zhenga1/Anodroid/Process Solidworks Version 6/2020-03-10_222859.png

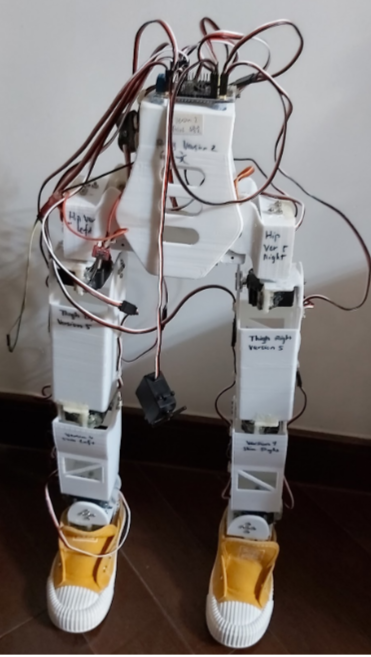
Process Solidworks Version 6/2020-03-10_222859.png
