zhenga1/Anodroid/Process Solidworks Version 6/Motor assem new with axis.SLDASM

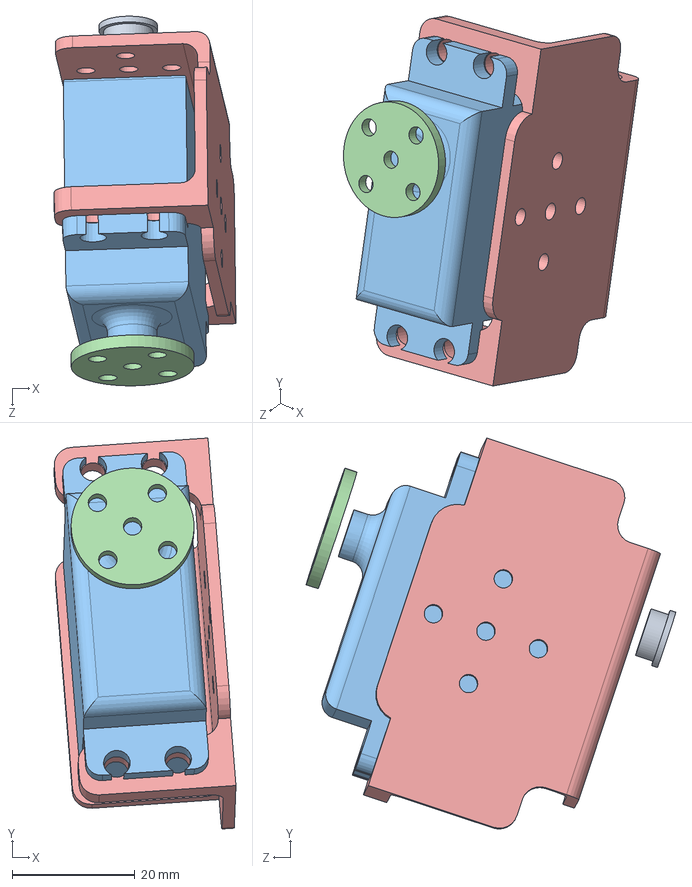
[picture p9: CAD file, 2020-06-27]
Process Solidworks Version 6/Motor assem new with axis.SLDASM
29.6 x 63.6 x 60.1 mm
Holder Right
Top of motor-SR1501
Motor SR-1501
Assisting axis part
Major Axis
