zhenga1/Anodroid/Process Solidworks Newest/Motor assem new with axis.SLDASM

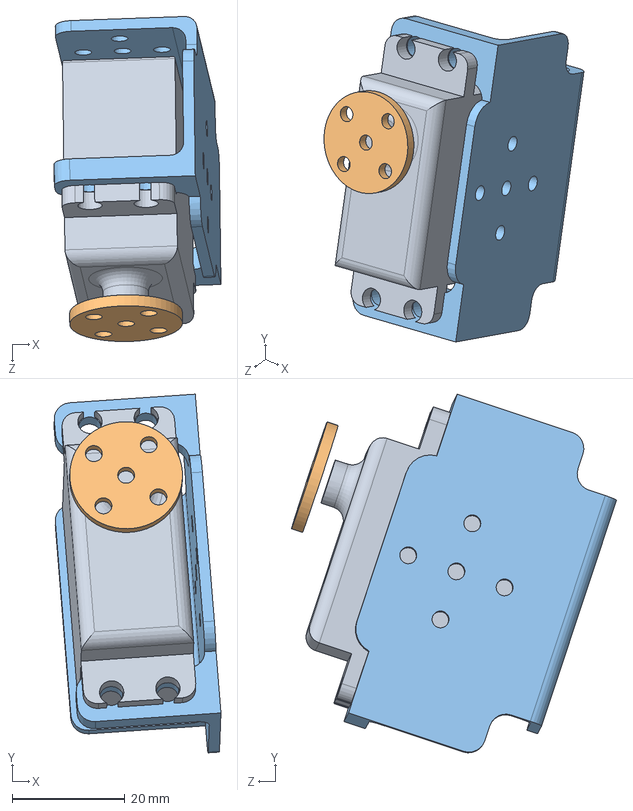
[picture p14: CAD file, 2020-06-27]
Process Solidworks Newest/Motor assem new with axis.SLDASM
29.6 x 63.6 x 57.6 mm
Holder Right
Top of motor-SR1501
Motor SR-1501
