zhenga1/Anodroid/Process Solidworsk version 3(incomplete)/Assemcomplete.SLDASM

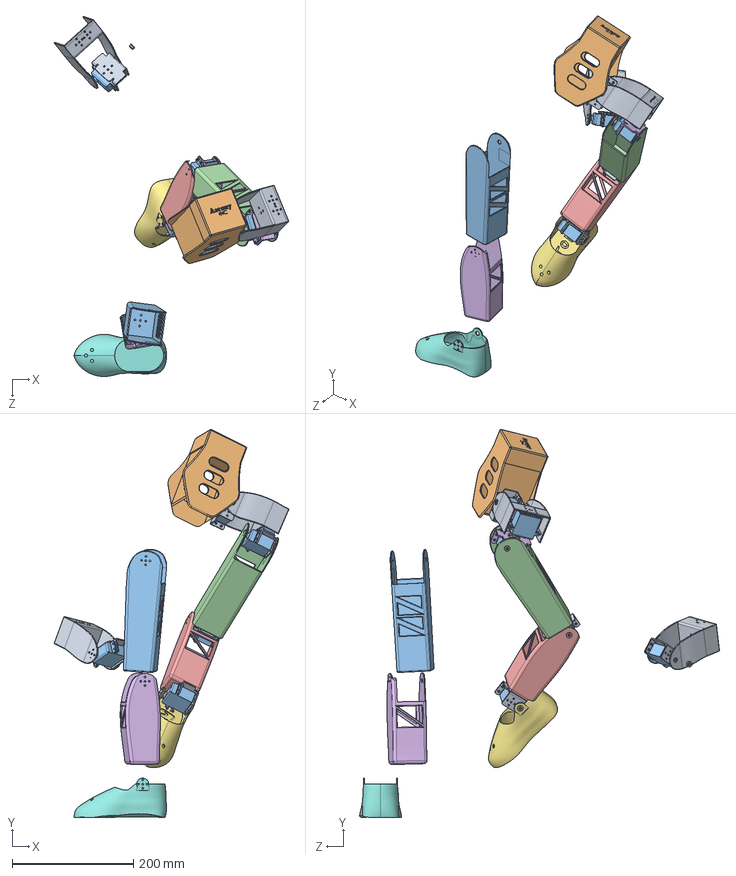
[picture p22: CAD file, 2020-06-27]
Process Solidworsk version 3(incomplete)/Assemcomplete.SLDASM
386.8 x 639.6 x 593.3 mm
pelvisthing
Thigh left
ThighFirst
Shinmy
Shincpy
Foot
Foot left
Holder x 5
Top of motor-SR1501 x 6
Motor SR-1501 x 6
Assisting axis part x 4
Major Axis x 5
Holder - Copy
