zhenga1/Anodroid/Process Solidworks Version 6/Replacement Temporary.SLDASM

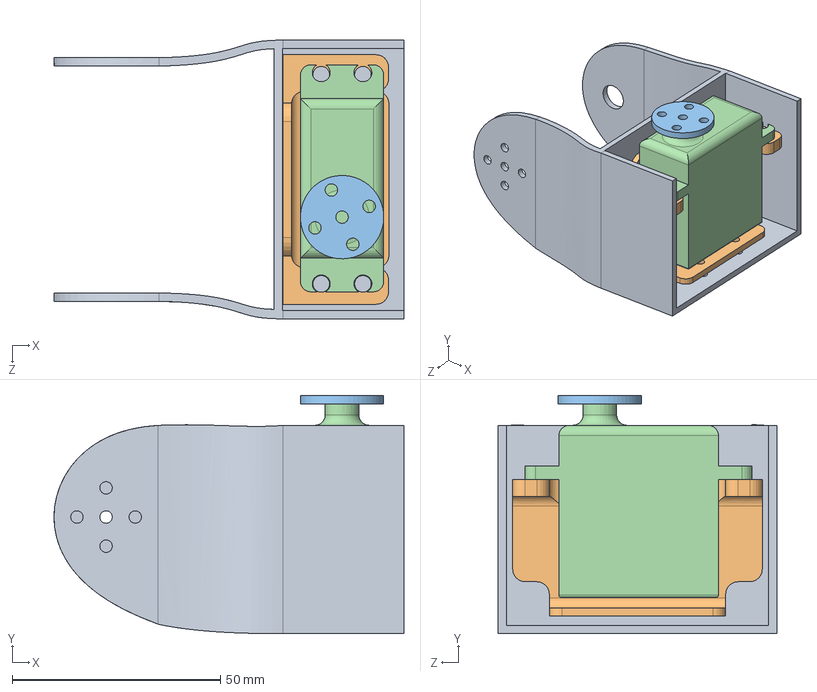
[picture p23: CAD file, 2020-06-27]
Process Solidworks Version 6/Replacement Temporary.SLDASM
84.0 x 57.2 x 66.9 mm
hip v5
Holder Right
Top of motor-SR1501
Motor SR-1501
