zhenga1/Anodroid/Process Solidworks Version 6/Motor assem modified right.SLDASM

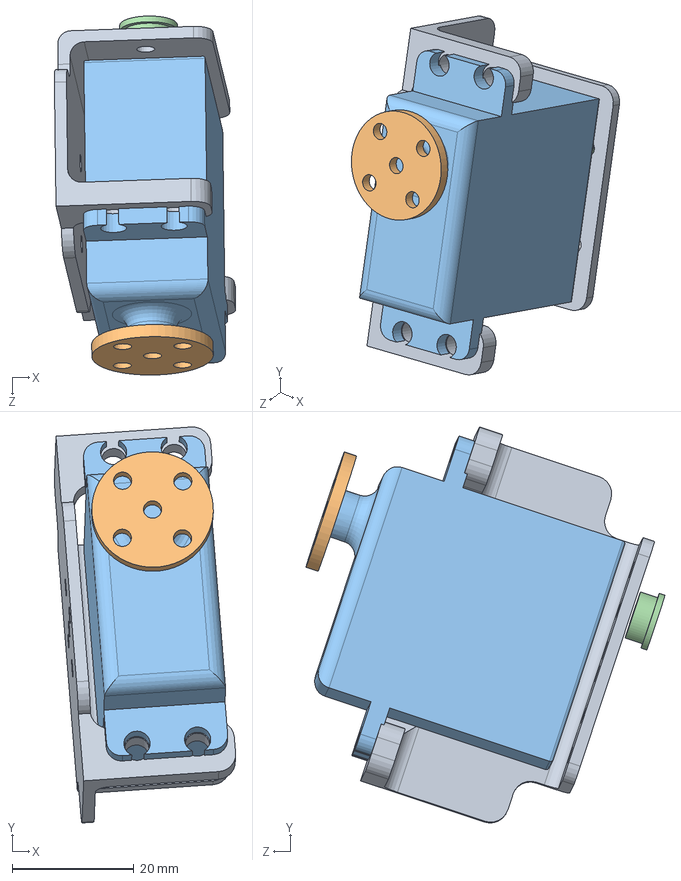
[picture p24: CAD file, 2020-06-27]
Process Solidworks Version 6/Motor assem modified right.SLDASM
29.8 x 65.1 x 59.1 mm
Top of motor-SR1501
Motor SR-1501
Holder Left
Major Axis
