zhenga1/Anodroid/Process Solidworks Newest/Hip-test-main.SLDASM

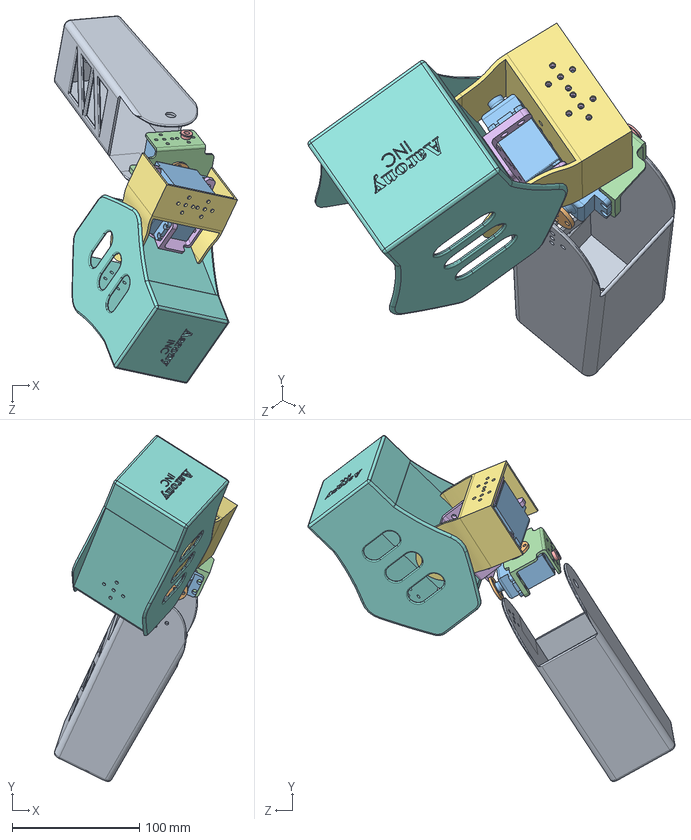
[picture p25: CAD file, 2020-06-27]
Process Solidworks Newest/Hip-test-main.SLDASM
143.9 x 271.9 x 288.4 mm
ThighFirst
Top of motor-SR1501 x 3
Motor SR-1501 x 3
Holder - Copy
Major Axis
Holder x 2
pelvisthing
