zhenga1/Anodroid/Process Solidworks Version 6/Motor assem left.SLDASM

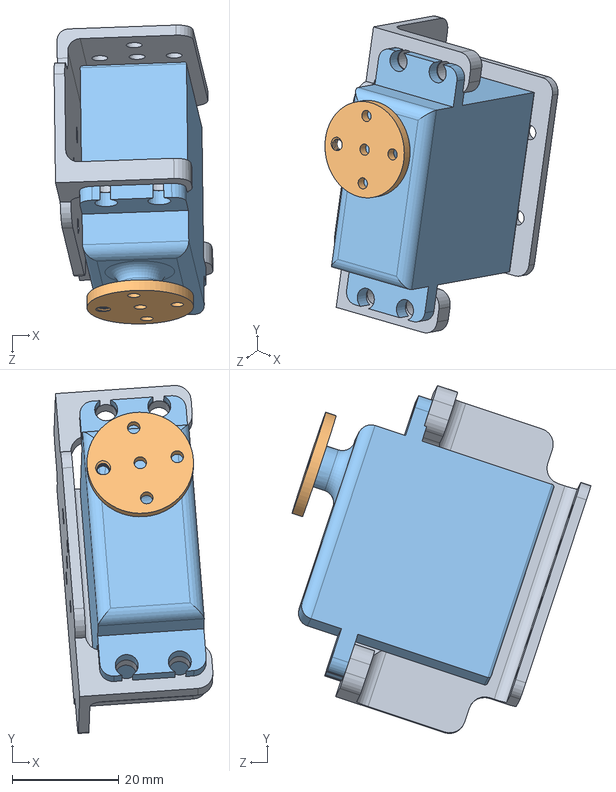
[picture p26: CAD file, 2020-06-27]
Process Solidworks Version 6/Motor assem left.SLDASM
29.8 x 65.3 x 56.1 mm
Top of motor-SR1501
Motor SR-1501
Holder Right
