zhenga1/Anodroid/Process Solidworsk version 3(incomplete)/Thigh Motor assem.SLDASM

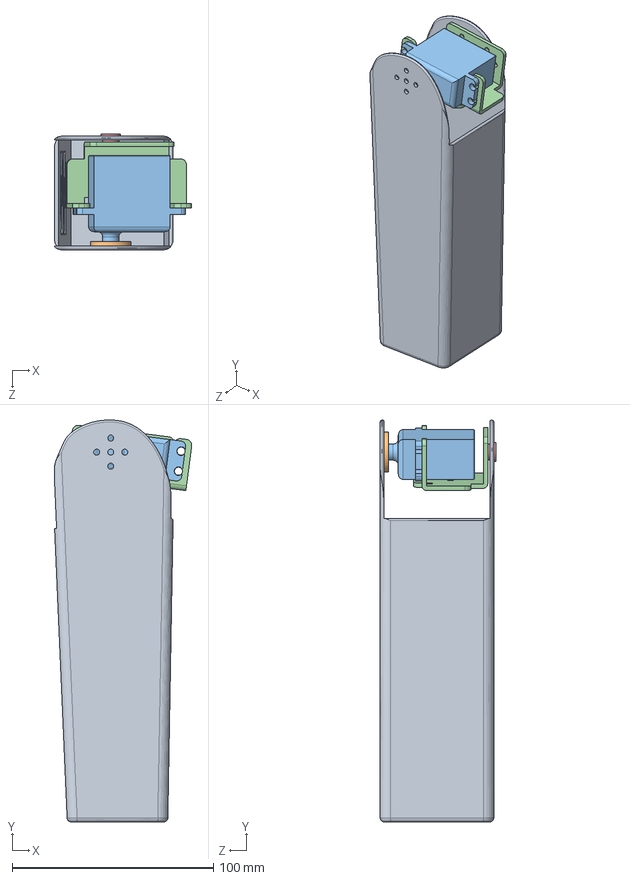
[picture p27: CAD file, 2019-08-12]
Process Solidworsk version 3(incomplete)/Thigh Motor assem.SLDASM
68.4 x 200.0 x 57.5 mm
ThighFirst
Top of motor-SR1501
Motor SR-1501
Holder - Copy
Major Axis
