zhenga1/Anodroid/Process Solidworsk version 3(incomplete)/Shincpy.SLDPRT

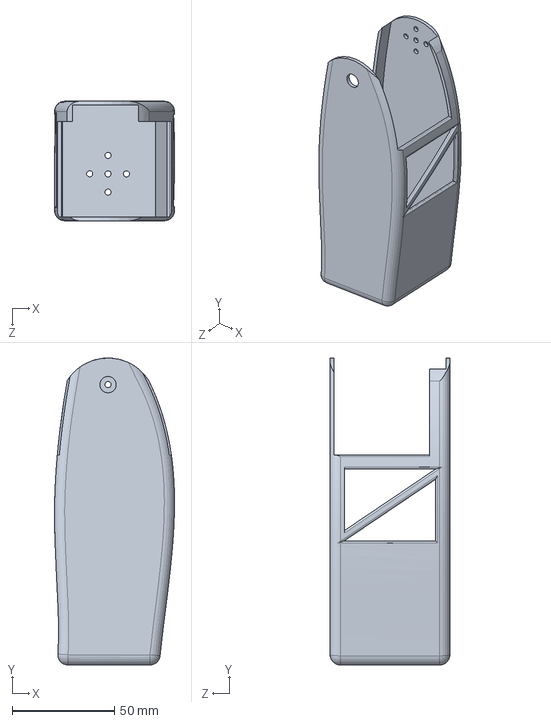
[picture p28: CAD file, 2020-06-27]
Process Solidworsk version 3(incomplete)/Shincpy.SLDPRT
58.7 x 150.0 x 58.5 mm
