zhenga1/Anodroid/Process Solidworks Version 6/hip v6.SLDPRT

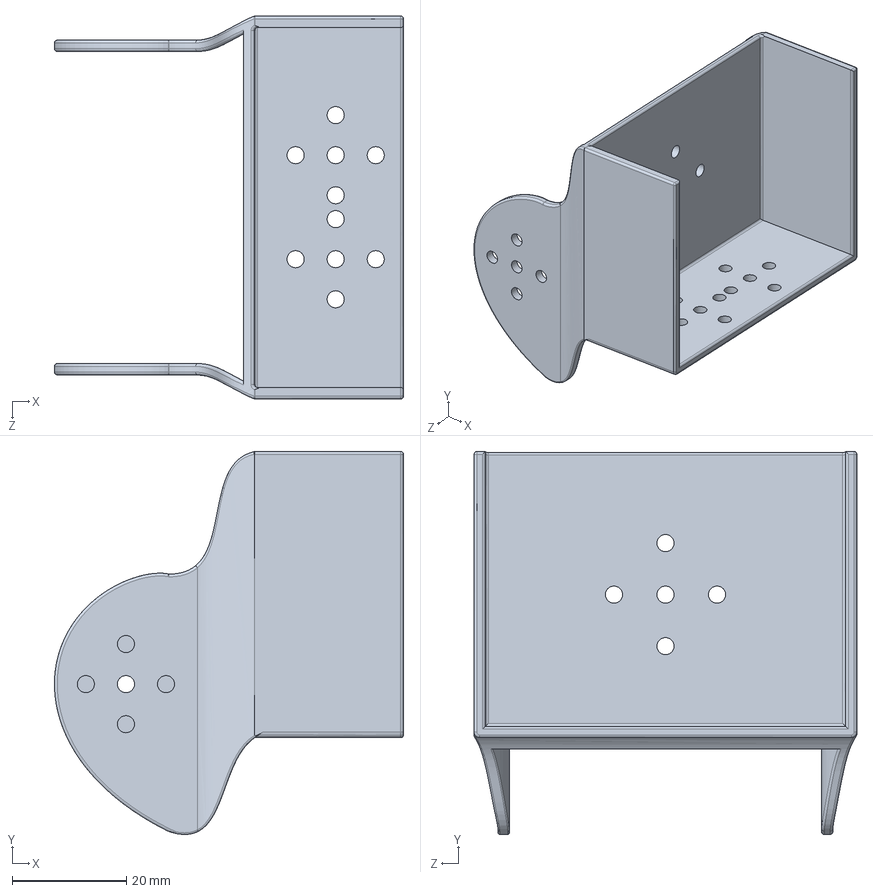
[picture p29: CAD file, 2020-06-27]
Process Solidworks Version 6/hip v6.SLDPRT
61.0 x 66.9 x 66.9 mm
