zhenga1/Anodroid/Process Solidworsk version 3(incomplete)/Foot.SLDPRT

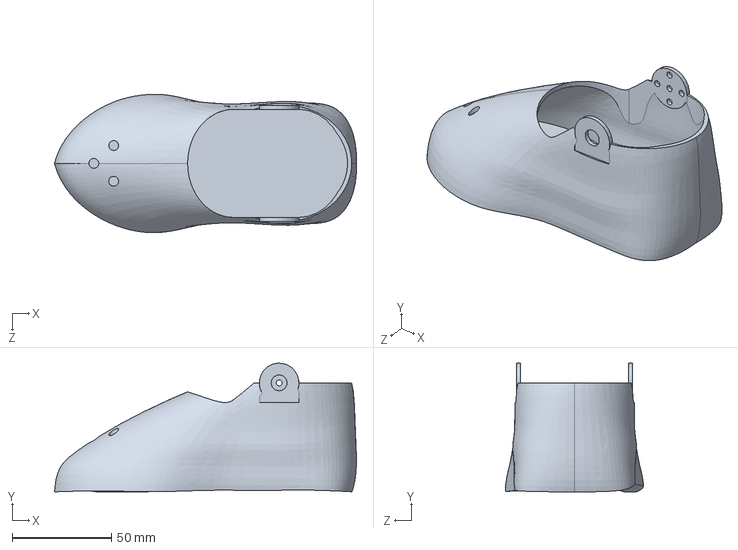
[picture p30: CAD file, 2020-06-27]
Process Solidworsk version 3(incomplete)/Foot.SLDPRT
152.4 x 65.0 x 69.8 mm
