zhenga1/Anodroid/Process Solidworks Version 6/pelvisthing.SLDPRT

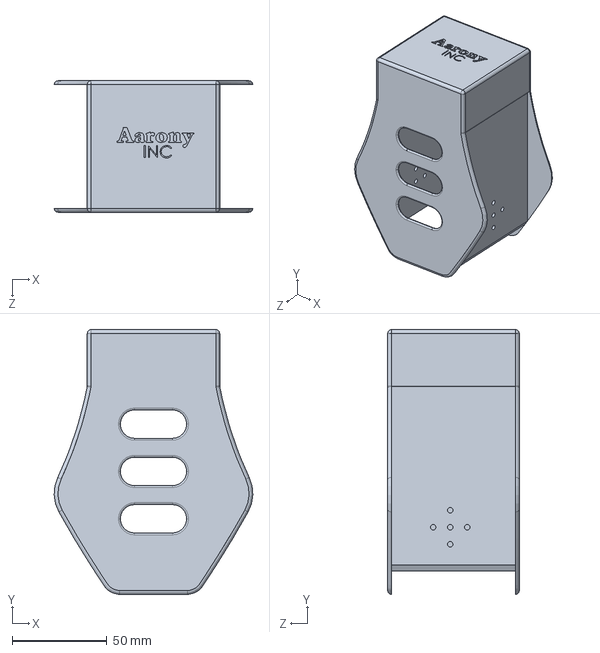
[picture p31: CAD file, 2020-06-27]
Process Solidworks Version 6/pelvisthing.SLDPRT
105.0 x 140.0 x 69.5 mm
