zhenga1/Anodroid/Process Solidworks Newest/Shincpy.SLDPRT

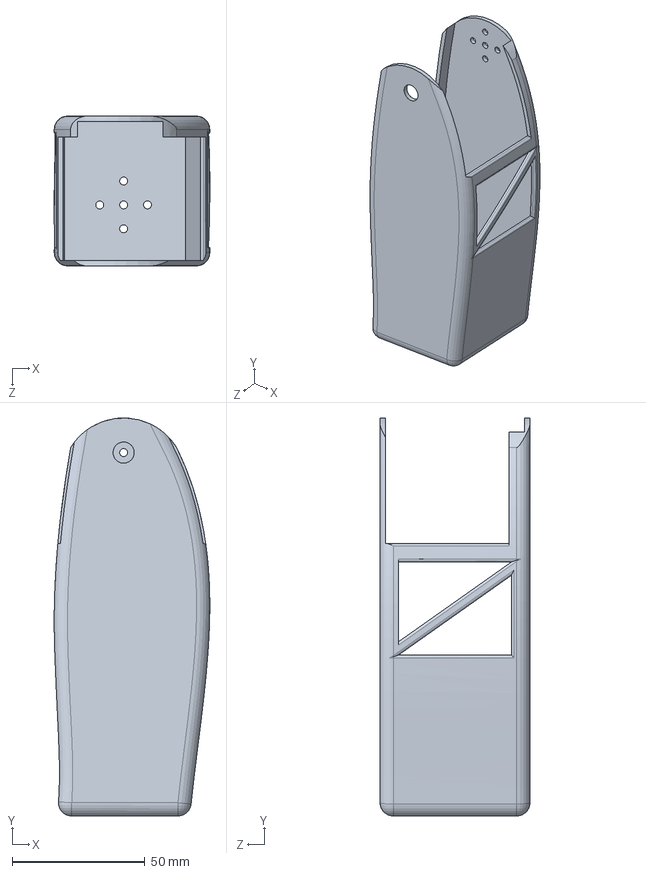
[picture p32: CAD file, 2020-06-27]
Process Solidworks Newest/Shincpy.SLDPRT
58.7 x 150.0 x 56.5 mm
