zhenga1/Anodroid/Process Solidworks Version 6/Holder Left.SLDPRT

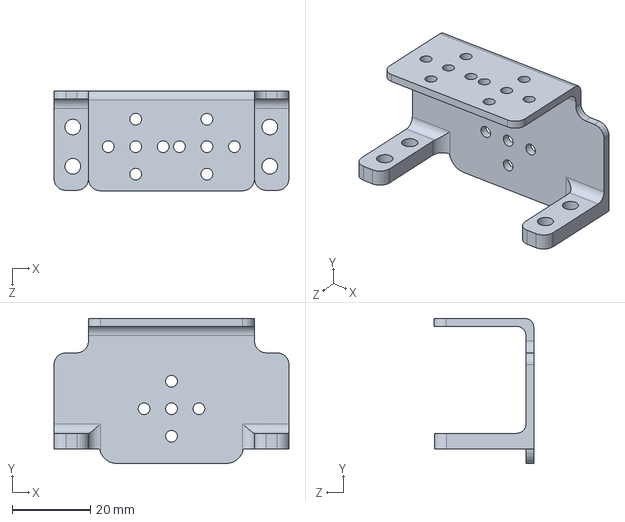
[picture p33: CAD file, 2020-06-27]
Process Solidworks Version 6/Holder Left.SLDPRT
59.9 x 37.0 x 25.4 mm
