zhenga1/Anodroid/Process Solidworsk version 3(incomplete)/Holder.SLDPRT

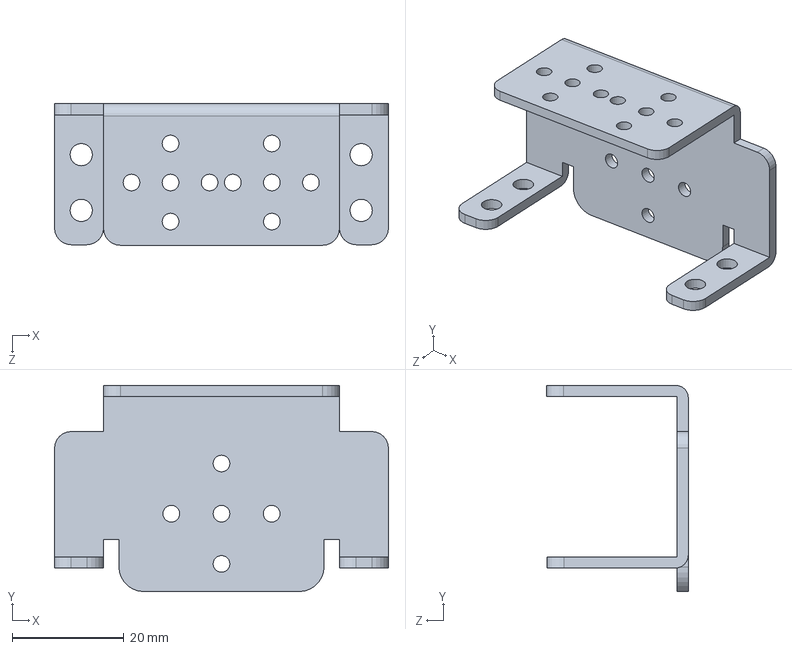
[picture p34: CAD file, 2020-06-27]
Process Solidworsk version 3(incomplete)/Holder.SLDPRT
59.9 x 37.0 x 25.4 mm
