zhenga1/Anodroid/Process Solidworks Version 6/Footconnectorpieceleft.SLDPRT

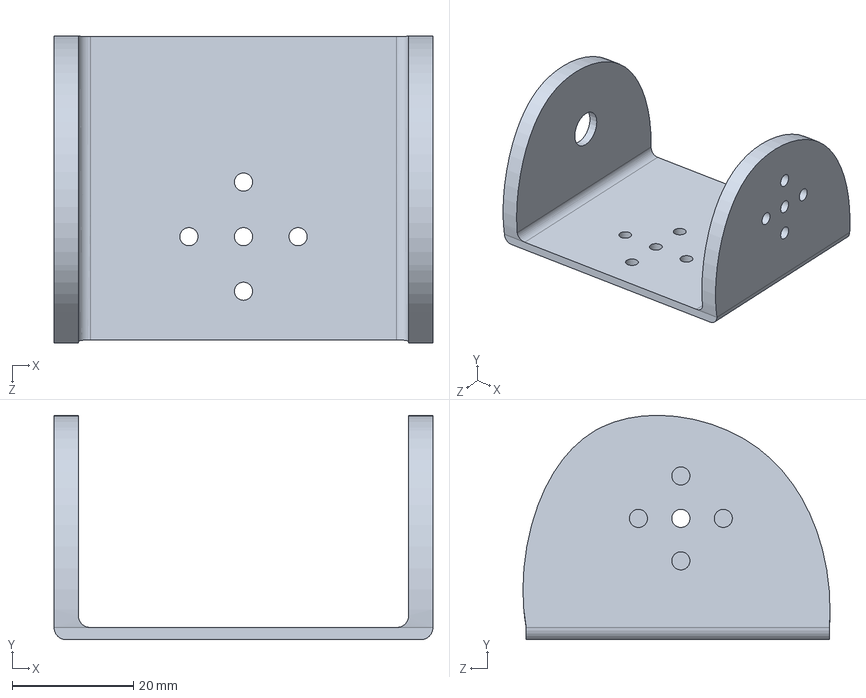
[picture p35: CAD file, 2020-06-27]
Process Solidworks Version 6/Footconnectorpieceleft.SLDPRT
62.5 x 37.0 x 50.7 mm
