zhenga1/Anodroid/Process Solidworsk version 3(incomplete)/Thigh left.SLDPRT

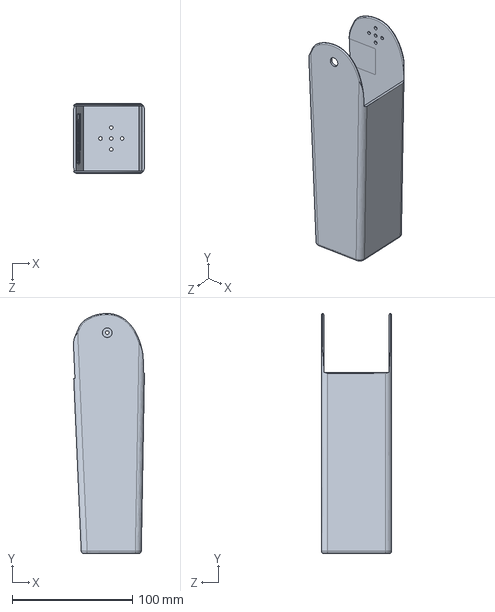
[picture p36: CAD file, 2020-06-27]
Process Solidworsk version 3(incomplete)/Thigh left.SLDPRT
59.1 x 200.0 x 58.5 mm
