zhenga1/Anodroid/Process Solidworks Newest/Motor SR-1501.SLDPRT

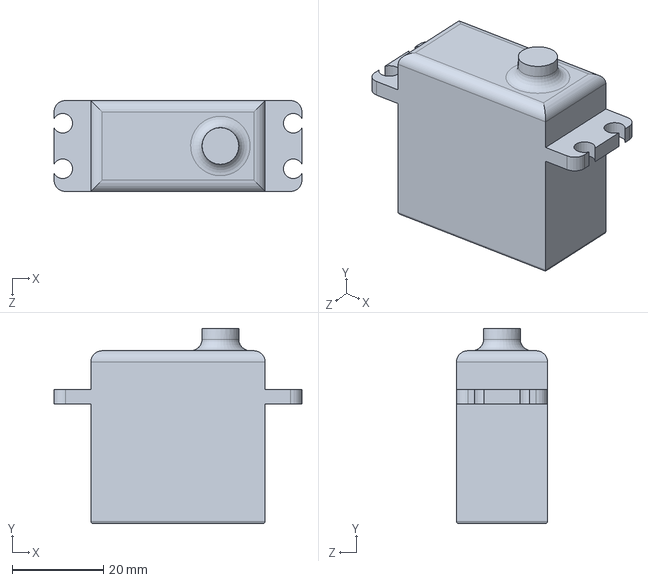
[picture p37: CAD file, 2020-06-27]
Process Solidworks Newest/Motor SR-1501.SLDPRT
54.5 x 42.9 x 20.0 mm
