zhenga1/Anodroid/Process Solidworks Version 6/ThighFirst.SLDPRT

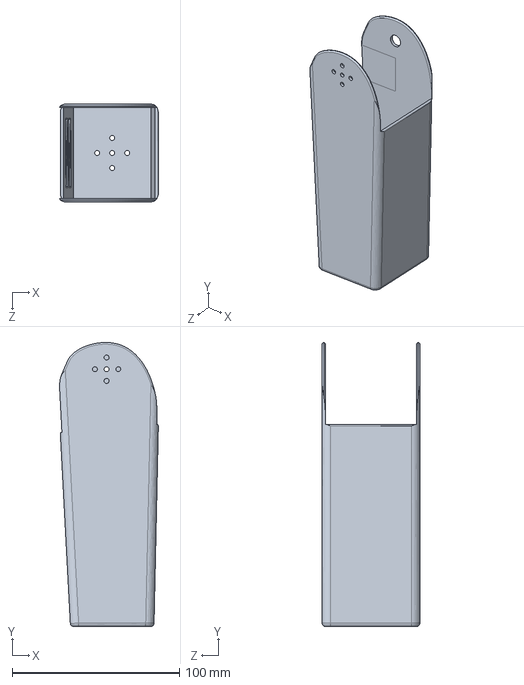
[picture p38: CAD file, 2020-06-27]
Process Solidworks Version 6/ThighFirst.SLDPRT
59.1 x 170.0 x 58.5 mm
