zhenga1/Anodroid/Process Solidworsk version 3(incomplete)/Part1.SLDPRT

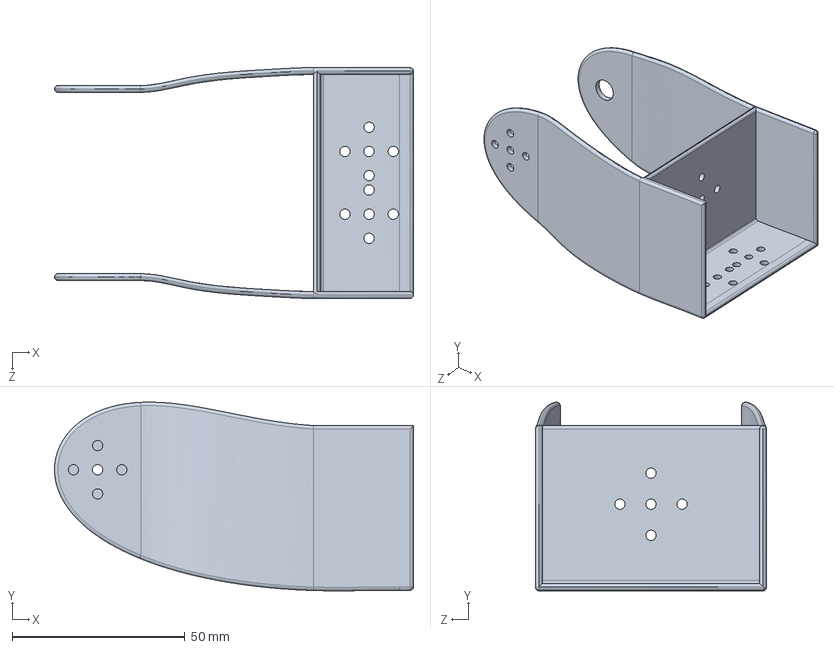
[picture p39: CAD file, 2020-06-27]
Process Solidworsk version 3(incomplete)/Part1.SLDPRT
104.0 x 54.7 x 66.9 mm
