zhenga1/Anodroid/Process Solidworsk version 3(incomplete)/Assisting axis part.SLDPRT

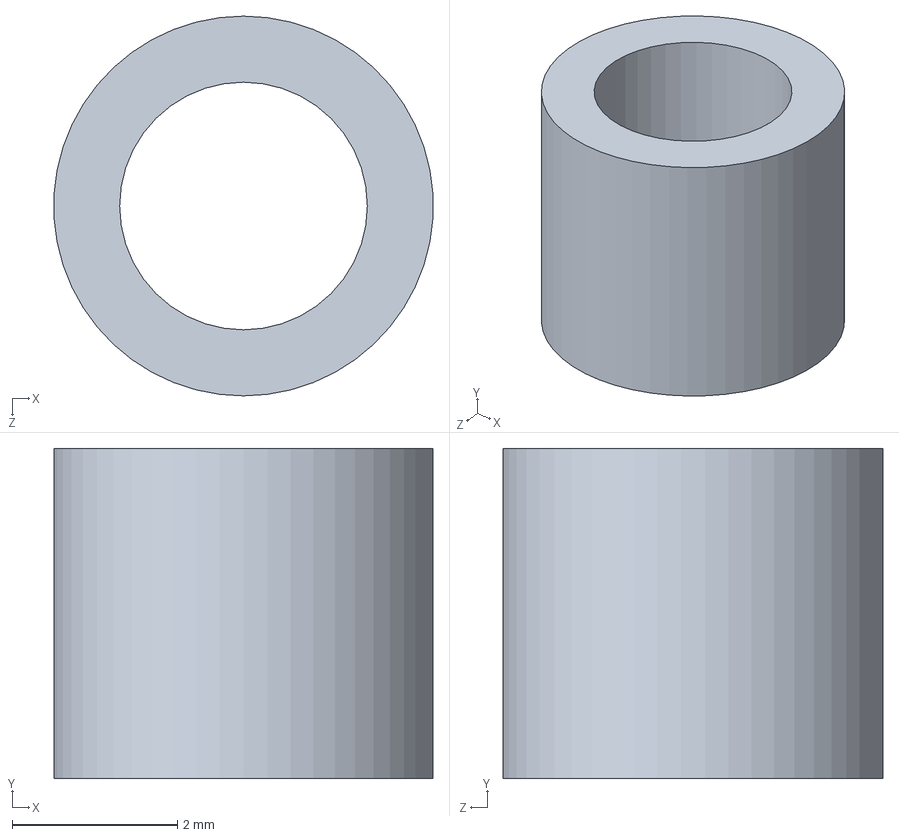
[picture p40: CAD file, 2019-08-12]
Process Solidworsk version 3(incomplete)/Assisting axis part.SLDPRT
4.59 x 4.00 x 4.60 mm
