zhenga1/Anodroid/Process Solidworks Newest/hip v5 past.SLDPRT

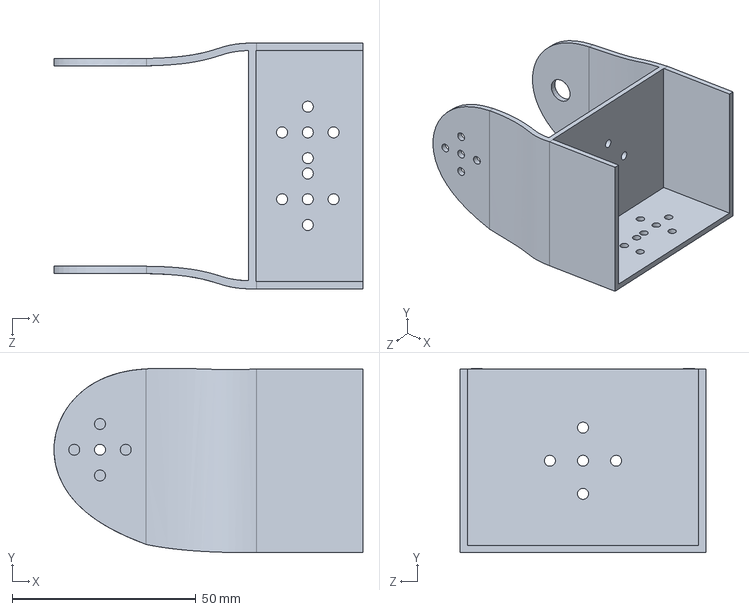
[picture p41: CAD file, 2020-06-27]
Process Solidworks Newest/hip v5 past.SLDPRT
84.0 x 50.1 x 66.9 mm
