zhenga1/Anodroid/Process Solidworks Version 6/Lengthenedfootconnectorpart.SLDPRT

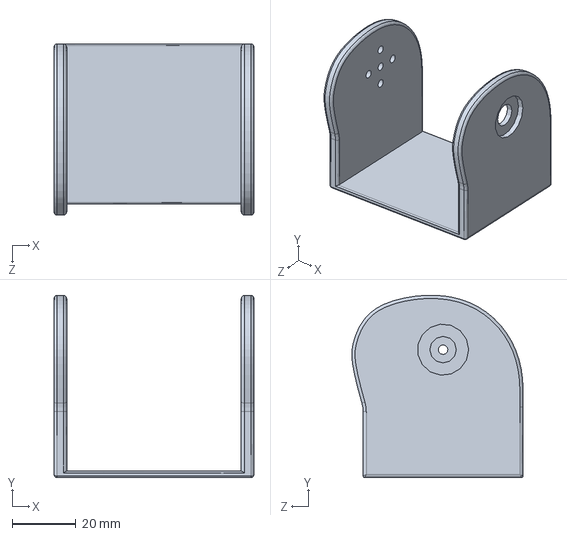
[picture p42: CAD file, 2020-06-27]
Process Solidworks Version 6/Lengthenedfootconnectorpart.SLDPRT
62.5 x 57.0 x 53.6 mm
