zhenga1/Anodroid/Process Solidworsk version 3(incomplete)/Top of motor-SR1501.SLDPRT

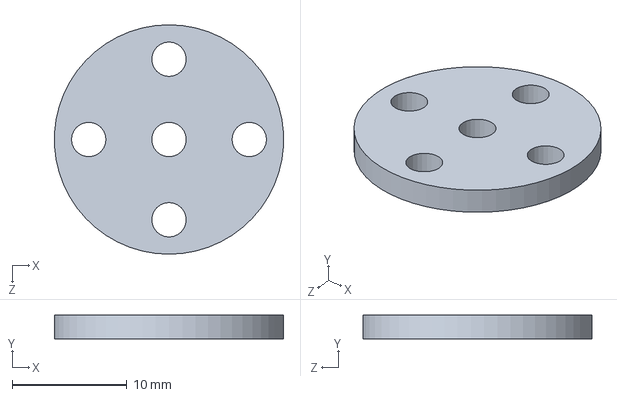
[picture p43: CAD file, 2019-08-12]
Process Solidworsk version 3(incomplete)/Top of motor-SR1501.SLDPRT
20.0 x 2.06 x 20.0 mm
