zhenga1/Anodroid/Process Solidworsk version 3(incomplete)/Major Axis.SLDPRT

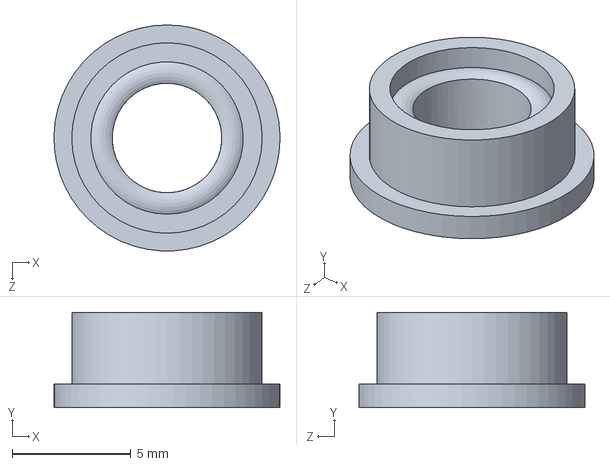
[picture p44: CAD file, 2019-08-12]
Process Solidworsk version 3(incomplete)/Major Axis.SLDPRT
9.50 x 4.00 x 9.50 mm
