zhenga1/Anodroid/Process Solidworks Version 6/Shincpy.SLDPRT

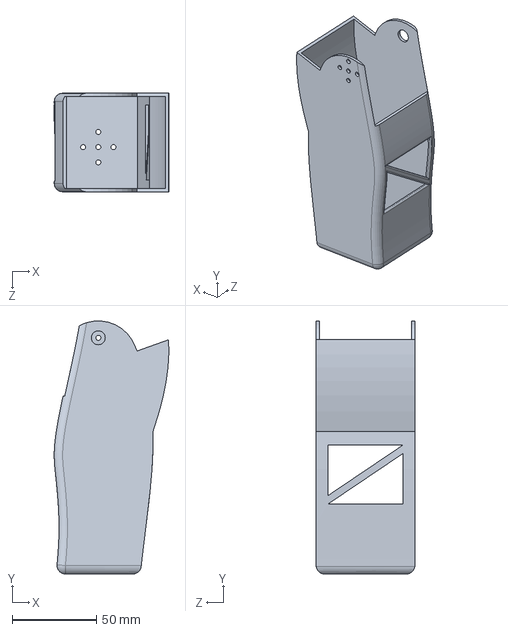
[picture p45: CAD file, 2020-06-27]
Process Solidworks Version 6/Shincpy.SLDPRT
68.0 x 150.0 x 58.5 mm
