zhenga1/Anodroid/Process Solidworks Newest/Foot left.SLDPRT

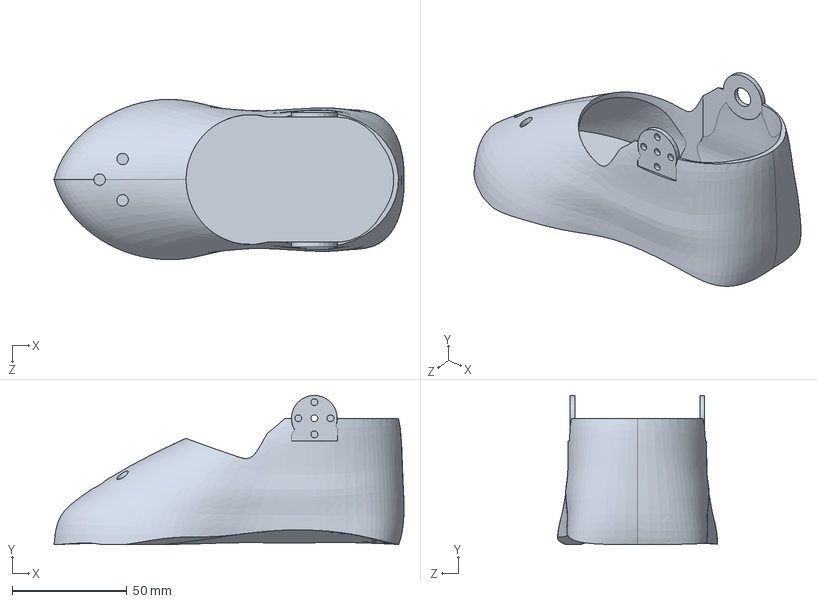
[picture p46: CAD file, 2019-08-12]
Process Solidworks Newest/Foot left.SLDPRT
152.4 x 65.0 x 69.8 mm
