zhenga1/Anodroid/Process Solidworks Newest/Foot right.SLDPRT

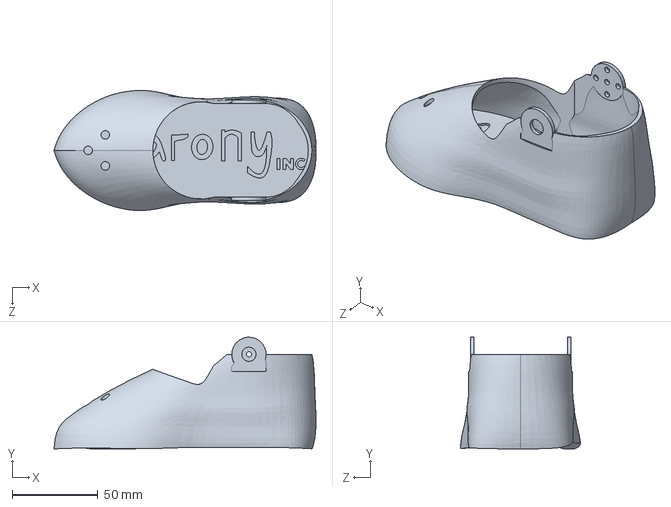
[picture p47: CAD file, 2019-08-12]
Process Solidworks Newest/Foot right.SLDPRT
152.4 x 65.0 x 69.8 mm
